Stephane-Peel/OBS-Keyb4Derby/Pictures To publish/20220429_190544_redimensionner.jpg

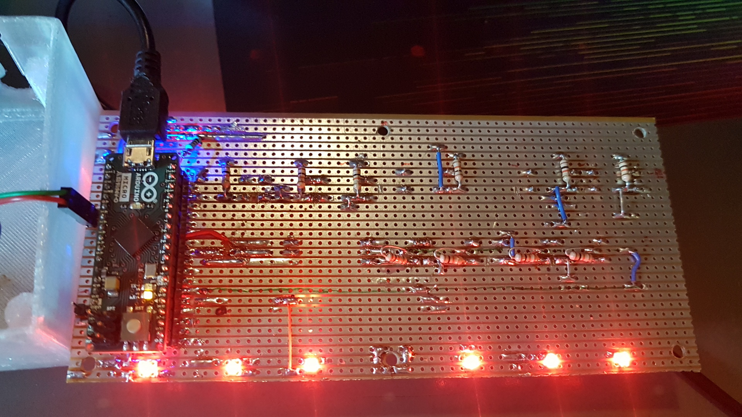
Pictures To publish/20220429_190544_redimensionner.jpg
