Stephane-Peel/OBS-Keyb4Derby/Schematics/OBS-Keyb.sch

## EAGLE design Schematics/OBS-Keyb.sch (2022-04-29)

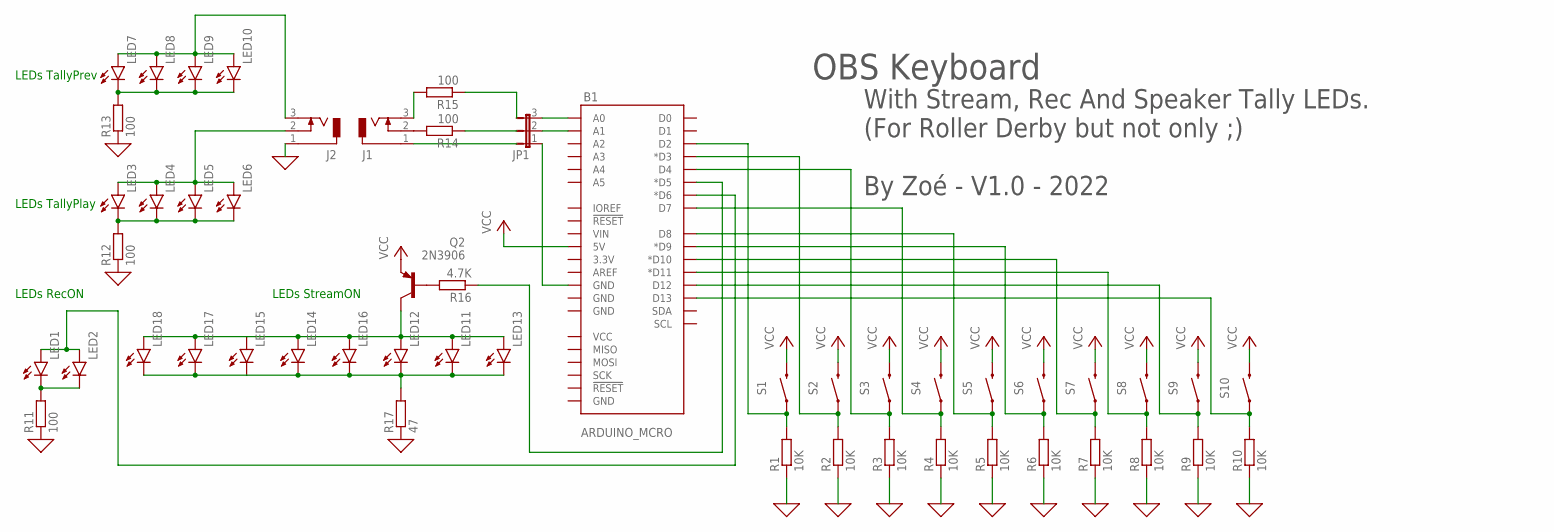
[picture p14: schematic OBS-Keyb.sch]

Parts:
B1: ARDUINO_MCRO; ARDUINO_R3
J1, J2: DCJ0303
JP1: JP2E; JP2
LED1, LED2, LED3, LED4, LED5, LED6, LED7, LED8, LED9, LED10, LED11, LED12, LED13, LED14, LED15, LED16, LED17, LED18: LEDCHIPLED_0805; CHIPLED_0805
Q2: 2N3906; TO92
R1, R2, R3, R4, R5, R6, R7, R8, R9, R10: 10K; 0204/5
R11, R12, R13, R14, R15: 100; 0204/5
R16: 4.7K; 0204/5
R17: 47; 0204/5
S1, S2, S3, S4, S5, S6, S7, S8, S9, S10: MOMENTARY-SWITCH-SPST-PTH-6.0MM; TACTILE_SWITCH_PTH_6.0MM

Connections:
0: J2.1, R1.1, R2.1, R3.1, R4.1, R5.1, R6.1, R7.1, R8.1, R9.1, R10.1, R11.1, R12.1, R13.1, R17.1
unnamed: B1.D2, R1.2, S1.1
unnamed: B1.D3 (*D3), R2.2, S2.1
unnamed: B1.D4, R3.2, S3.1
unnamed: B1.D7, R4.2, S4.1
unnamed: B1.D8, R5.2, S5.1
unnamed: B1.D9 (*D9), R6.2, S6.1
unnamed: B1.D10 (*D10), R7.2, S7.1
unnamed: B1.D11 (*D11), R8.2, S8.1
unnamed: B1.D12, R9.2, S9.1
unnamed: B1.D13, R10.2, S10.1
unnamed: LED1.C, LED2.C, R11.2
unnamed: LED17.C, LED18.C
unnamed: LED3.C, LED4.C, LED5.C, LED6.C, R12.2
unnamed: J2.2, LED3.A, LED4.A, LED5.A, LED6.A
unnamed: B1.A0, JP1.3
unnamed: B1.A1, JP1.2
unnamed: LED7.C, LED8.C, LED9.C, LED10.C, R13.2
unnamed: J2.3, LED7.A, LED8.A, LED9.A, LED10.A
unnamed: B1.GND@4 (GND), JP1.1
unnamed: J1.2, R14.2
unnamed: J1.3, R15.2
unnamed: LED17.A, LED18.A
unnamed: Q2.2 (B), R16.2
unnamed: LED11.C, LED12.C, LED13.C, LED14.C, LED15.C, LED16.C, R17.2
unnamed: LED11.A, LED12.A, LED13.A, LED14.A, LED15.A, LED16.A, Q2.1 (C)
unnamed: B1.D5 (*D5), R16.1
unnamed: B1.D6 (*D6), LED1.A, LED2.A
VCC: B1.5V, Q2.3 (E), S1.3 (2), S2.3 (2), S3.3 (2), S4.3 (2), S5.3 (2), S6.3 (2), S7.3 (2), S8.3 (2), S9.3 (2), S10.3 (2)

Notes on the sheet:
LEDs StreamON
LEDs RecON
LEDs TallyPrev
LEDs TallyPlay
With Stream, Rec And Speaker Tally LEDs. (For Roller Derby but not only ;) By Zoé - V1.0 - 2022
OBS Keyboard
